Derek-Mc/Enviroment-Station/Project Website/project.jpg

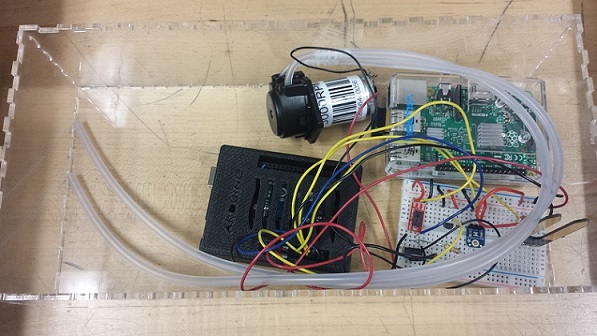
Project Website/project.jpg
