Derek-Mc/Enviroment-Station/Project Website/sensors2.jpg

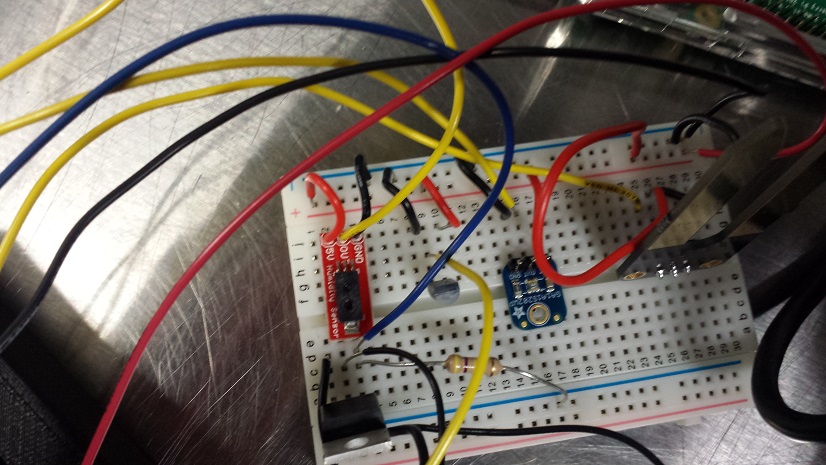
Project Website/sensors2.jpg
